sTeeLM/NeoIVClock/Doc/TPM300/IMG_9310.JPG

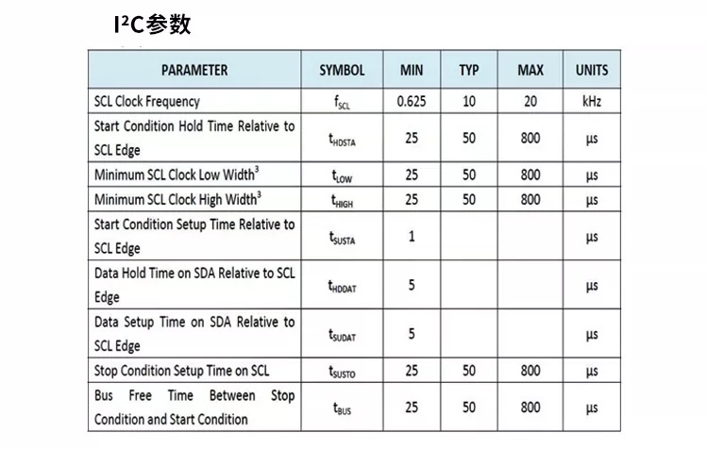
Doc/TPM300/IMG_9310.JPG
