sTeeLM/NeoIVClock/Doc/TPM300/IMG_9311.JPG

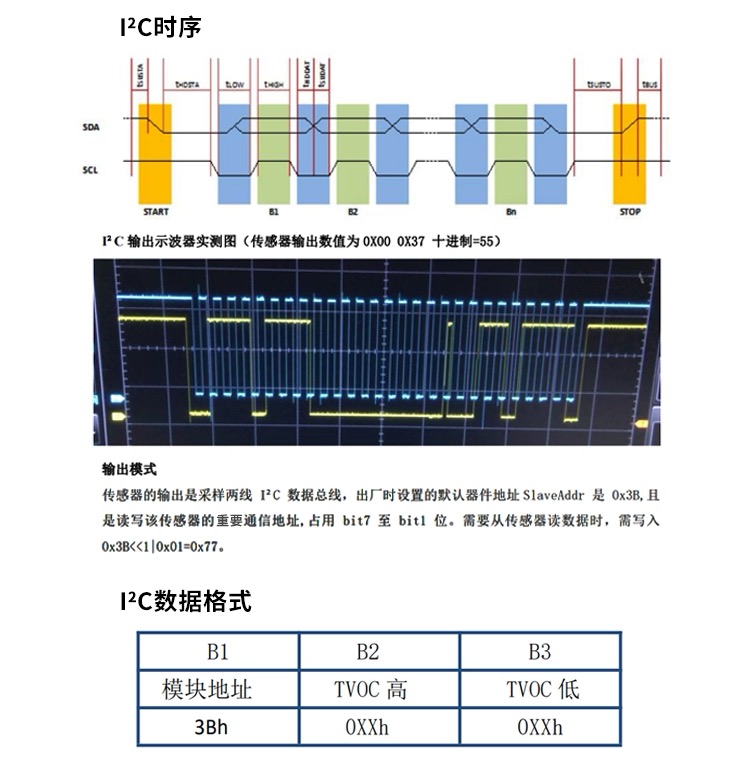
Doc/TPM300/IMG_9311.JPG
