sTeeLM/NeoIVClock/Doc/TPM300/IMG_9312.JPG

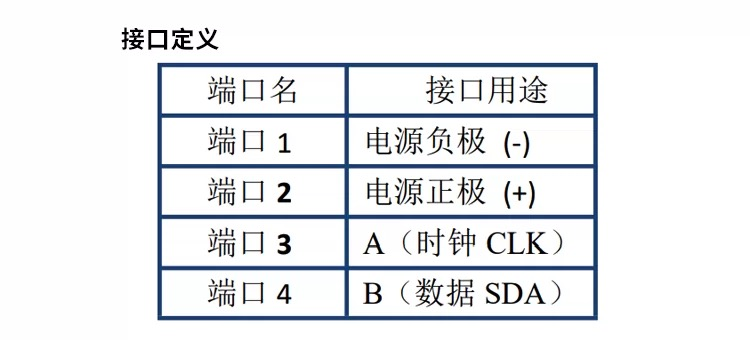
Doc/TPM300/IMG_9312.JPG
