sTeeLM/NeoIVClock/Doc/TPM300/IMG_9313.JPG

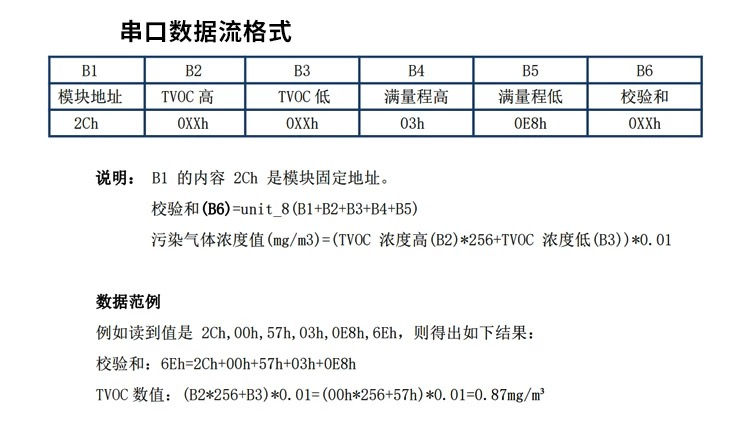
Doc/TPM300/IMG_9313.JPG
