sTeeLM/NeoIVClock/Doc/YD-ESP32/ESP32-size-m.png

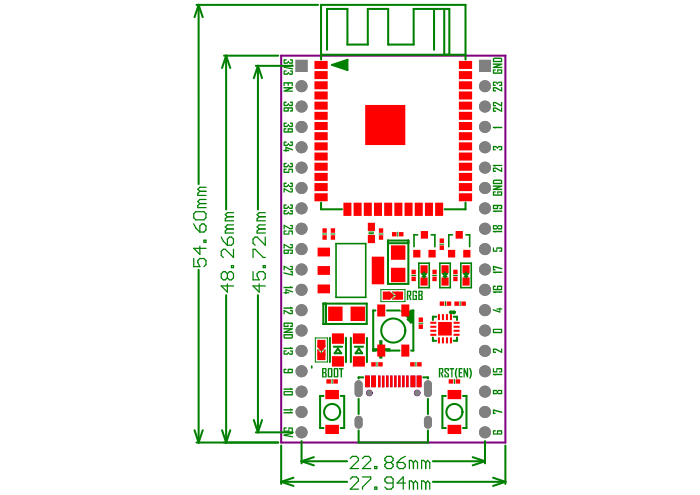
Doc/YD-ESP32/ESP32-size-m.png
