sTeeLM/NeoIVClock/Src/NeoIVClock/components/iv18/iv18.c

#include "iv18.h"
#include "clock.h"
#include "config.h"
#include "logger.h"
#include "clock.h"
#include "gpio_wrapper.h"
#include "cext.h"
#include "light_sensor.h"

#include "driver/ledc.h"

#define IV18_DP    0x40
#define IV18_BLINK 0x20000

static uint8_t  iv18_cur_index;
static uint16_t  iv18_cur_loop;
static uint32_t iv18_data[9];

// 自动亮度控制
// IV18_ADC_MAX -> IV18_BRIGHT_AUTO_MAX
// IV18_ADC_MIN -> IV18_BRIGHT_AUTO_MIN
#define IV18_ADC_MAX  3000
#define IV18_ADC_MIN  200
#define IV18_BRIGHT_AUTO_MAX 100
#define IV18_BRIGHT_AUTO_MIN 5
#define IV18_MAX_BRIGHTNESS  100
#define IV18_BRIGHT_FAST_STEP 10
static uint8_t iv18_brightness;
static uint8_t iv18_brightness_auto;
static uint8_t iv18_enabled;

// Power Save: 其实更多是为了延长IV18的寿命
static uint32_t iv18_now_sec;
/*
  0:关闭 1:10s，2:30s，3:1分钟
*/
static uint8_t iv18_ps_timeo;

static const char * TAG = "IV18";

/*
Out0  G9
Out1  G1
Out2  G3
Out3  G5
Out4  G8
Out5  G7
Out6  G6
Out7  G4
Out8  G2
Out9  a
Out10 dp
Out11 d
Out12 c
Out13 e
Out14 g
Out15 b
Out16 f

   a
f     b
   g
e     c
   d    dp
*/

/*
   -------------|b|scan code|8 dig code
   000000000000000|000000000|0d000000
   b: blink
*/



static const uint16_t iv18_scan_code[9] = 
{
  0x100, // 100000000 
  0x010, // 000010000 
  0x008, // 000001000
  0x004, // 000000100
  0x020, // 000100000
  0x002, // 000000010
  0x040, // 001000000
  0x001, // 000000001  
  0x080, // 010000000
};

static const uint8_t iv18_dig_special[] =
{
        /* aPdcegbf */
   0x00, //00000000  BLANK
   0x87, //10000111  o  degree assume ascii 1!! 
   0x82, //10000010  progress 0,ab
   0x06, //00000110  progress 1,bg
   0x0c, //00001100  progress 2,ge 
   0x28, //00101000  progress 3,ed
   0x30, //00110000  progress 4,dc
   0x14, //00010100  progress 5,cg
   0x05, //00000101  progress 6,gf
   0x81, //10000001  progress 7,fa
};

static const uint8_t iv18_dig_ascii[] =
{
        /* aPdcegbf */
   0x04, //00000100  -  ascii: 0x2D
   0x00, //00000000  .
   0x00, //00000000  /
   0xBB, //10111011  0    
   0x12, //00010010  1
   0xAE, //10101110  2
   0xB6, //10110110  3
   0x17, //00010111  4
   0xB5, //10110101  5
   0xBD, //10111101  6
   0x93, //10010011  7
   0xBF, //10111111  8
   0xB7, //10110111  9
   0x00, //00000000  :
   0x00, //00000000  ;
   0x28, //00101000  <
   0x24, //00100100  =  
   0x30, //00110000  >
   0x00, //00000000  ?
   0x00, //00000000  @
   
        /* aPdcegbf */   
   0x9F, //10011111  A
   0x3D, //00111101  B
   0xA9, //10101001  C
   0x3E, //00111110  D
   0xAD, //10101101  E
   0x8D, //10001101  F
   0xB9, //10111001  G
   0x1F, //00011111  H
   0x09, //00001001  I
   0x32, //00110010  J 
   0x00, //00000000  K
   0x29, //00101001  L
   0x15, //00010101  M
   0x9B, //10011011  N
   0x3C, //00111100  O
   0x8F, //10001111  P
   0x97, //10010111  Q
   0x0C, //00001100  R
   0xB5, //10110101  S == 5
   0x2D, //00101101  T
   0x3B, //00111011  U
   0x70, //01110000  V
   0x0E, //00001110  W
   0x00, //00000000  X
   0x0F, //00001111  Y
   0x00, //00000000  Z ascii 0x5A
};

static void iv18_show_data(uint32_t data)
{
  uint8_t i;

  for(i = 0 ; i < 17 ; i ++) {   
    gpio_wrapper_set_level(IV18_DIN_GPIO_PIN, (data & 0x1) ? 1 : 0);
    gpio_wrapper_set_level(IV18_CLK_GPIO_PIN, 1);
    gpio_wrapper_set_level(IV18_CLK_GPIO_PIN, 0);
    data >>= 1;
  }
  gpio_wrapper_set_level(IV18_LOAD_GPIO_PIN, 1);
  gpio_wrapper_set_level(IV18_LOAD_GPIO_PIN, 0);
};

void iv18_scan(void)
{
  uint32_t empty;
  if(iv18_data[ iv18_cur_index] & IV18_BLINK) {
    if( iv18_cur_loop % 64 < 32) {
      iv18_load_data( iv18_cur_index);
    } else {
      empty = iv18_data[ iv18_cur_index];
      empty &= 0x1FF40; // keep scan code and dp
      iv18_show_data(empty);
    }
  } else {
    iv18_load_data( iv18_cur_index);
  }
   iv18_cur_index ++;
   iv18_cur_index %= 9;
  if( iv18_cur_index == 8)
     iv18_cur_loop ++;
}

static void iv18_dev_init(void)
{
  uint8_t i;
  
  memset(iv18_data, 0, sizeof(iv18_data));
  
  for(i = 0 ; i < 9 ; i ++)
    iv18_set_dig(i, 0);
  
  iv18_set_dig(2, 'H');
  iv18_load_data(2);
  iv18_set_dig(3, 'E'); 
  iv18_load_data(3);  
  iv18_set_dig(4, 'L');
  iv18_load_data(4);   
  iv18_set_dig(5, 'L'); 
  iv18_load_data(5);   
  iv18_set_dig(6, 'O'); 
  iv18_load_data(6);   
  
  iv18_cur_index = 0;
  iv18_cur_loop = 0;
}

static void iv18_set_brightness_internal(uint8_t level);

void iv18_init(void)
{
  // Prepare and then apply the LEDC PWM timer configuration
  ledc_timer_config_t ledc_timer = {
        .speed_mode       = LEDC_LOW_SPEED_MODE,
        .duty_resolution  = LEDC_TIMER_13_BIT,
        .timer_num        = LEDC_TIMER_0,
        .freq_hz          = 4000, // Frequency in Hertz. Set frequency at 4 kHz
        .clk_cfg          = LEDC_AUTO_CLK
  };
  
  // Prepare and then apply the LEDC PWM channel configuration
  ledc_channel_config_t ledc_channel = {
        .speed_mode     = LEDC_LOW_SPEED_MODE,
        .channel        = LEDC_CHANNEL_0,
        .timer_sel      = LEDC_TIMER_0,
        .intr_type      = LEDC_INTR_DISABLE,
        .gpio_num       = IV18_BLANK_GPIO_PIN,
        .duty           = 0, // Set duty to 0%
        .hpoint         = 0
  };

  NEO_LOGI(TAG, "init");
  
  gpio_wrapper_set_level(IV18_EN_GPIO_PIN, 0);
  gpio_wrapper_set_level(IV18_CLK_GPIO_PIN, 0);
  gpio_wrapper_set_level(IV18_DIN_GPIO_PIN, 0);
  gpio_wrapper_set_level(IV18_LOAD_GPIO_PIN, 0);
  gpio_wrapper_set_level(IV18_BLANK_GPIO_PIN, 0);
  
  ESP_ERROR_CHECK(ledc_timer_config(&ledc_timer));
  ESP_ERROR_CHECK(ledc_channel_config(&ledc_channel));

  iv18_enabled = false;

  iv18_enable(true);

  iv18_brightness = config_read_int("iv18_brightness") % (IV18_MAX_BRIGHTNESS + 1);
  iv18_set_brightness_internal(iv18_brightness);
  iv18_brightness_auto = 0;

  iv18_ps_timeo = config_read_int("iv18_ps_sec") % 4;

  iv18_dev_init();
}

void iv18_set_dig(uint8_t index, uint8_t code)
{
  uint32_t mask;
  if(index > 8)
    index = 8;

  mask = iv18_data[index] & (IV18_BLINK | IV18_DP);
  
  if(code >= 0x2D) {
    code = code - 0x2D;
    if(code >= sizeof(iv18_dig_ascii))
      code = sizeof(iv18_dig_ascii) - 1;
    iv18_data[index] = iv18_scan_code[index];
    iv18_data[index] <<= 8;
    iv18_data[index] |= iv18_dig_ascii[code];
    iv18_data[index] |= mask;    
  } else if(code <= IV18_SPECIAL_MAX) {
    if(code >= sizeof(iv18_dig_special))
      code = sizeof(iv18_dig_special) - 1;
    iv18_data[index] = iv18_scan_code[index];
    iv18_data[index] <<= 8;
    iv18_data[index] |= iv18_dig_special[code];
    iv18_data[index] |= mask;     
  } 
}

void iv18_set_dp(uint8_t index)
{
  if(index > 8)
    index = 8;
  
  iv18_data[index] |= IV18_DP;
}

void iv18_clr_dp(uint8_t index)
{
  if(index > 8)
    index = 8;
  
  iv18_data[index] &= ~IV18_DP;  
}

void iv18_set_blink(uint8_t index)
{
  if(index > 8)
    index = 8;
  
  iv18_data[index] |= IV18_BLINK;
}

void iv18_clr_blink(uint8_t index)
{
  if(index > 8)
    index = 8;
  
  iv18_data[index] &= ~IV18_BLINK;
}


void iv18_clr(void)
{
  uint8_t i;
  for(i = 0 ; i < 9 ; i++) {
    iv18_data[i] = iv18_scan_code[i];
    iv18_data[i] <<= 8; 
  }
}

void iv18_clr_data(uint8_t index)
{
  if(index > 8)
    index = 8;
  iv18_data[index] = iv18_scan_code[index];
  iv18_data[index] <<= 8;
}

void iv18_load_data(uint8_t index)
{
  if(index > 8)
    index = 8;
  iv18_show_data(iv18_data[index]);
}

void iv18_enable(bool enable)
{

  if((iv18_enabled && enable) || (!iv18_enabled && !enable))
    return;

  iv18_enabled = enable;

  gpio_wrapper_set_level(IV18_EN_GPIO_PIN, enable ? 1 : 0);

}

void iv18_set_brightness(uint8_t level)
{
  iv18_brightness = level % (IV18_MAX_BRIGHTNESS + 1);
  iv18_set_brightness_internal(level);
}

// level: 0~100, 0完全关闭，100完全打开
static void iv18_set_brightness_internal(uint8_t level)
{
  uint32_t duty;

  NEO_LOGD(TAG, "iv18_set_brightness: %d", level);

  // do nothing, IV18 has no brightness control
  if(level > IV18_MAX_BRIGHTNESS)
    level = IV18_MAX_BRIGHTNESS;

  if(level == IV18_MAX_BRIGHTNESS) {
    ESP_ERROR_CHECK(ledc_stop(LEDC_LOW_SPEED_MODE, LEDC_CHANNEL_0, 0));
    iv18_brightness_auto = 0;
  } else if(level == 0) {
    ESP_ERROR_CHECK(ledc_stop(LEDC_LOW_SPEED_MODE, LEDC_CHANNEL_0, 1));
    iv18_brightness_auto = 0;
  } else {
    duty = ((IV18_MAX_BRIGHTNESS - level) * 8191) / IV18_MAX_BRIGHTNESS; // 8191 is the max duty for 13-bit resolution
    ESP_ERROR_CHECK(ledc_set_duty(LEDC_LOW_SPEED_MODE, LEDC_CHANNEL_0, duty));
    ESP_ERROR_CHECK(ledc_update_duty(LEDC_LOW_SPEED_MODE, LEDC_CHANNEL_0));
  }
}

uint8_t iv18_get_brightness(void)
{
  return iv18_brightness;
}

// 每秒调用一次，如果iv18_brightness==0, 根据光线传感器调整亮度
void iv18_proc(task_event_t ev)
{
  int32_t val;
  uint16_t brightness;
  
  if(iv18_brightness == 0) {
    if( (val= light_sensor_read_data()) > 0) {
      if(val >= IV18_ADC_MAX)  {
        brightness = IV18_BRIGHT_AUTO_MAX;
      } else if(val <= IV18_ADC_MIN) {
        brightness = IV18_BRIGHT_AUTO_MIN;
      } else {
        brightness = cext_linear_interpolate(IV18_ADC_MAX, IV18_BRIGHT_AUTO_MAX, IV18_ADC_MIN, IV18_BRIGHT_AUTO_MIN, val);
      }
      if(brightness > IV18_BRIGHT_AUTO_MAX) brightness = IV18_BRIGHT_AUTO_MAX;
      if(brightness < IV18_BRIGHT_AUTO_MIN) brightness = IV18_BRIGHT_AUTO_MIN;
      NEO_LOGD(TAG, "iv18_brightness = %d, brightness = %d, iv18_brightness_auto = %d", iv18_brightness, brightness, iv18_brightness_auto);
      if(iv18_brightness_auto != brightness) {
        iv18_set_brightness_internal(brightness);
        iv18_brightness_auto = brightness;
      }
    }
  }
}

/*
0:关闭 1:10s，2:30s，3:1分钟
*/
static uint8_t iv8_get_ps_timeo_internal(void)
{
  switch (iv18_ps_timeo) {
    case 0: return 0;
    case 1: return 10;
    case 2: return 30;
    case 3: return 60; 
    default:
      NEO_LOGE(TAG, "invalid iv18_ps_timeo %d", iv18_ps_timeo);
    break;
  }
  return 0;
}

void iv18_test_ps_timeo(void)
{
  uint32_t diff;
  if(iv18_enabled) {
    if(iv8_get_ps_timeo()) {
      diff = clock_diff_now_sec(iv18_now_sec);
      if(diff > iv8_get_ps_timeo_internal()) {
        NEO_LOGD(TAG, "iv18_test_ps_timeo: time out");
        iv18_enable(false);
      }
    }
  }
}

uint8_t iv8_get_ps_timeo(void)
{
  return iv18_ps_timeo;
}

void iv18_reset_ps_timeo(void)
{
  iv18_now_sec = clock_get_now_sec();
  iv18_enable(true);
}

uint8_t iv18_inc_ps_sec(void)
{
  iv18_ps_timeo = (iv18_ps_timeo + 1) % 4;
  return iv18_ps_timeo;
}
void iv18_save_config(void)
{
  config_write_int("iv18_brightness", iv18_brightness);
  config_write_int("iv18_ps_sec", iv18_ps_timeo);
}

uint8_t iv18_inc_brightness(bool fast)
{
  iv18_brightness = iv18_brightness + (fast ? IV18_BRIGHT_FAST_STEP : 1);
  if(iv18_brightness > IV18_MAX_BRIGHTNESS)
    iv18_brightness = IV18_MAX_BRIGHTNESS;
  iv18_set_brightness_internal(iv18_brightness);
  return iv18_brightness;
}
uint8_t iv18_dec_brightness(bool fast)
{
  int16_t val = iv18_brightness;
  val -= fast ? IV18_BRIGHT_FAST_STEP : 1;
  if(val < 0)
    val = 0;
  iv18_brightness = val;

  iv18_set_brightness_internal(iv18_brightness);
  return iv18_brightness;
}

uint8_t iv18_get_max_brightness(void)
{
  return IV18_MAX_BRIGHTNESS;
}
